AHappyTeddy/LED-Cube-Build-Files/pics/20181116_221502.jpg

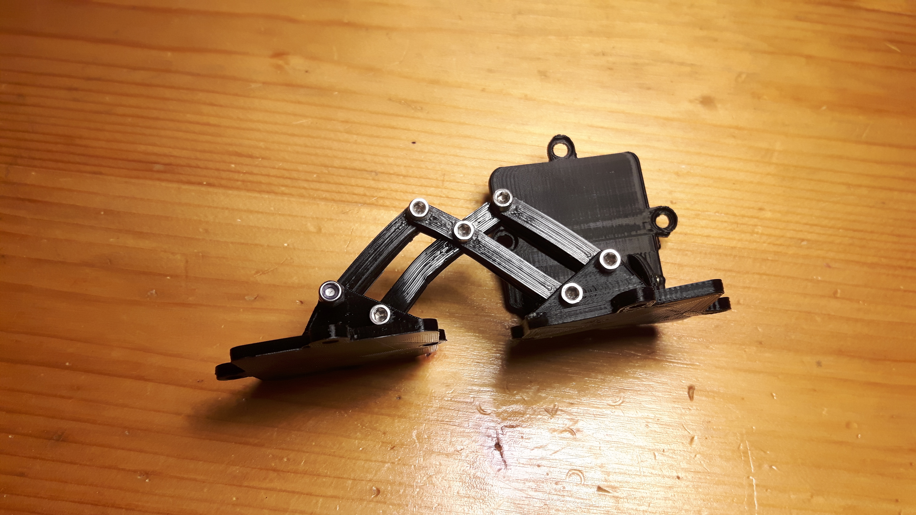
pics/20181116_221502.jpg
