AHappyTeddy/LED-Cube-Build-Files/pics/20181116_222600.jpg

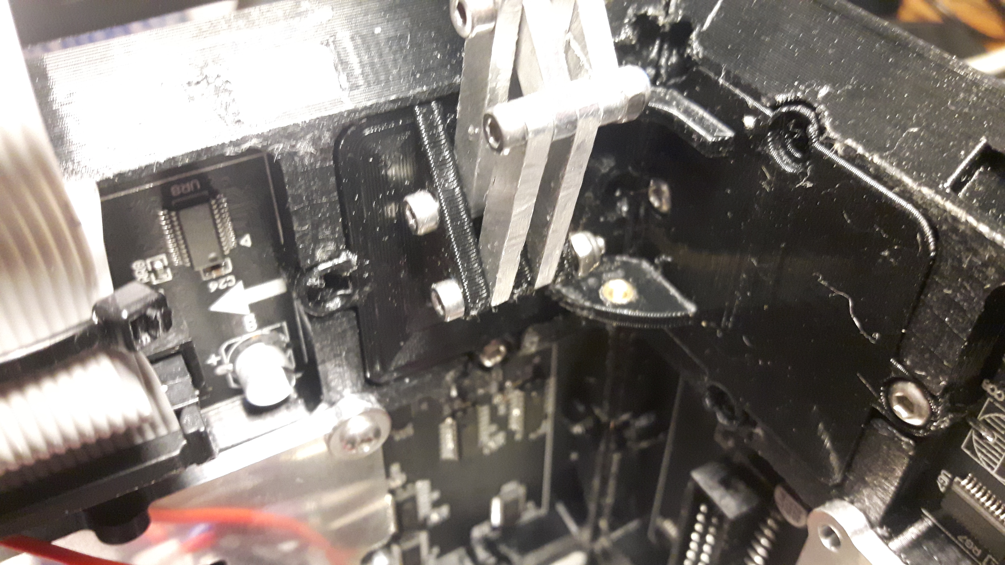
pics/20181116_222600.jpg
