AHappyTeddy/LED-Cube-Build-Files/STL_Files/8x_Handle1.stl

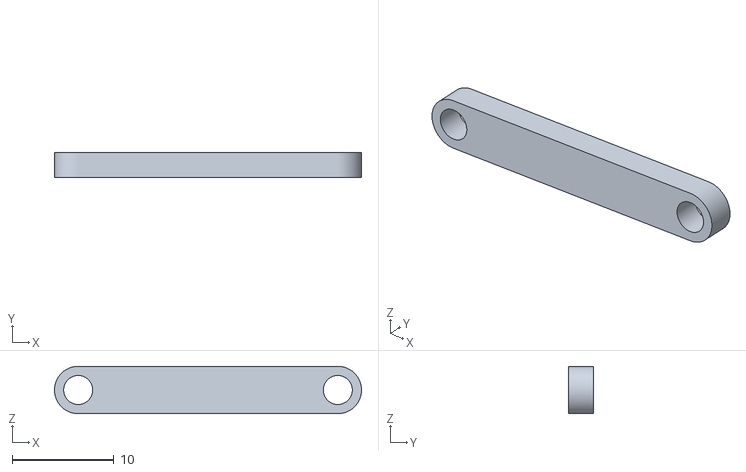
[picture p19: CAD file, 2018-11-16]
STL_Files/8x_Handle1.stl
30.2 x 2.50 x 4.65
